yan-h/lattice-board/firmware/controller/src/keys/mod.rs

#[cfg(feature = "layout-5x25")]
pub mod shift_reg;
#[cfg(feature = "layout-5x25")]
pub use shift_reg::*;

#[cfg(feature = "layout-prototype")]
pub mod direct;
#[cfg(feature = "layout-prototype")]
pub use direct::*;
